smaroukis/Segments-2-the-absurd/kicad/00-Assets-Datasheets/2024-05-27-v-alpha/level-shifter_Texas-Instruments-TXS0108EPWR_C17206.pdf_FOOTPRINT.png

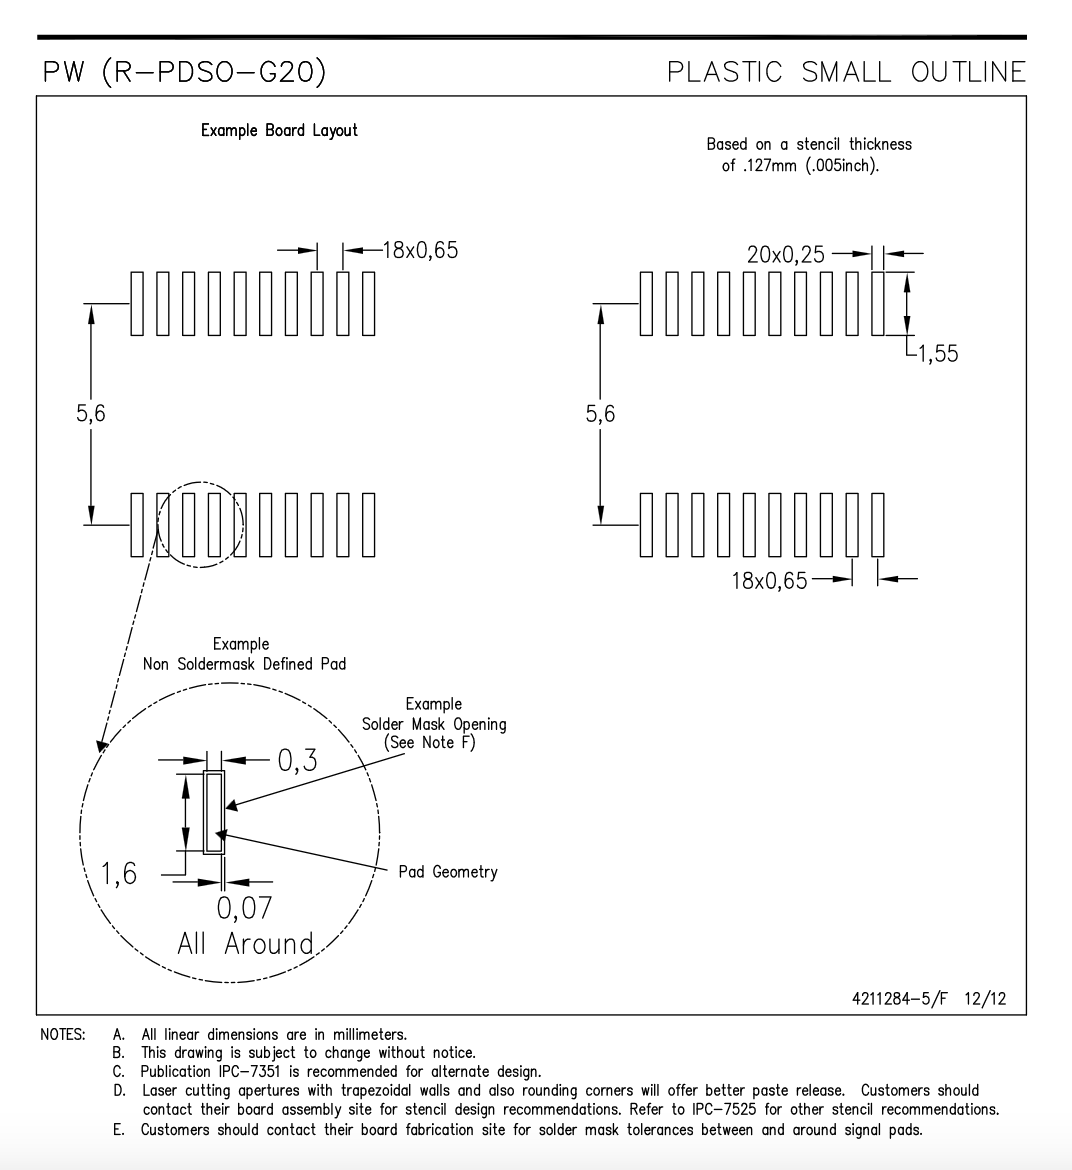
kicad/00-Assets-Datasheets/2024-05-27-v-alpha/level-shifter_Texas-Instruments-TXS0108EPWR_C17206.pdf_FOOTPRINT.png
