smaroukis/Segments-2-the-absurd/kicad/00-Assets-Datasheets/2024-05-27-v-alpha/mcu-STM32C011F6P6_C5456198_PACKAGE.png

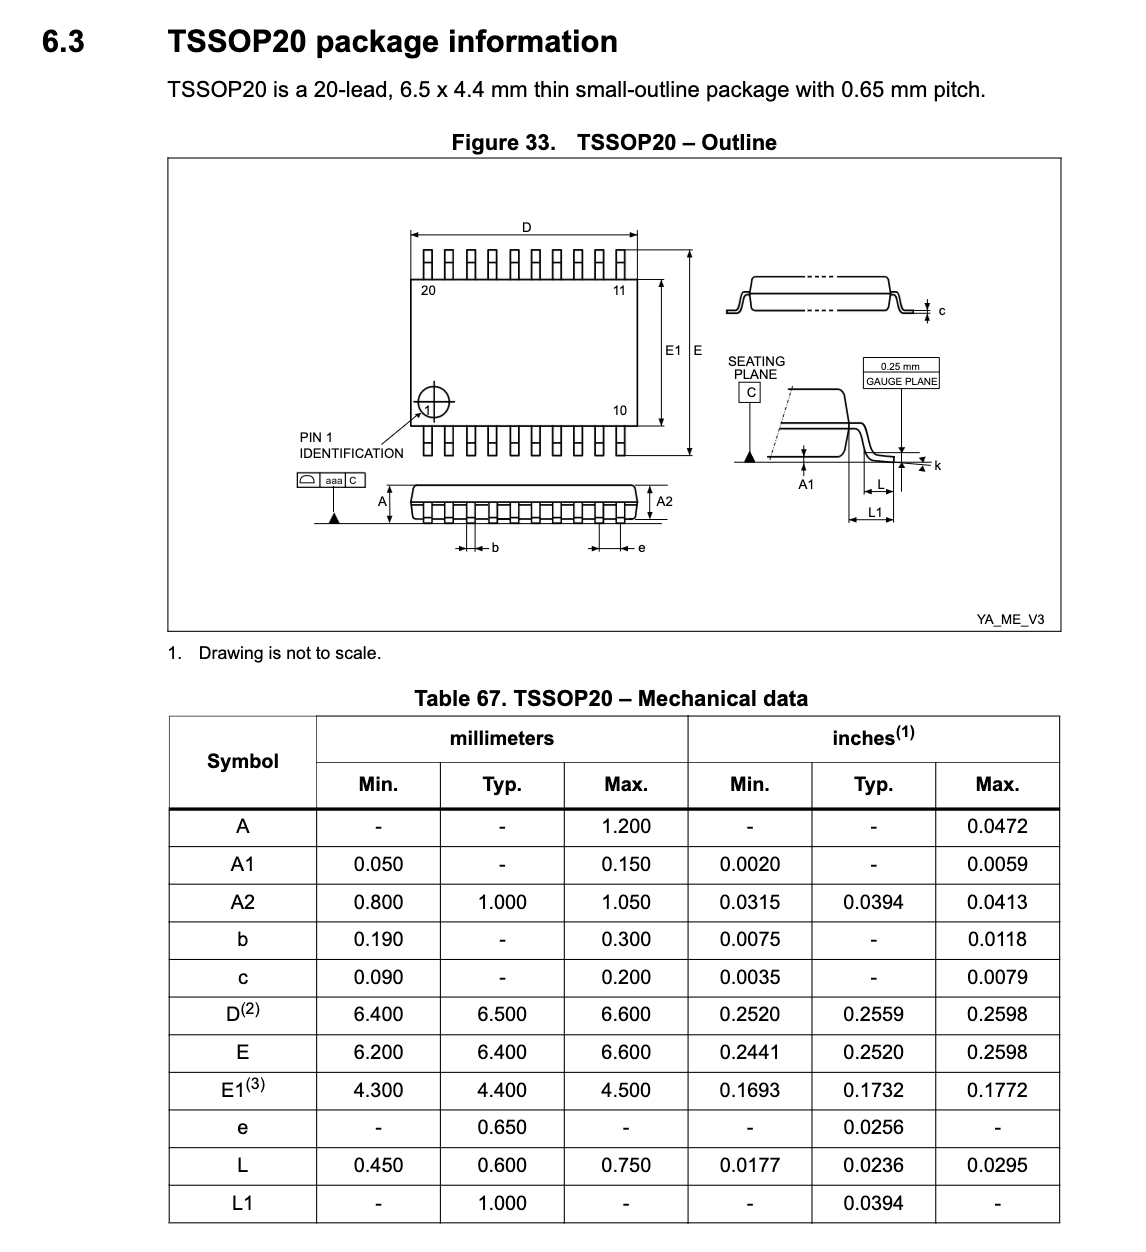
kicad/00-Assets-Datasheets/2024-05-27-v-alpha/mcu-STM32C011F6P6_C5456198_PACKAGE.png
