smaroukis/Segments-2-the-absurd/kicad/00-Assets-Datasheets/2024-05-27-v-alpha/sev-seg-driver_TM1637(TA2007)_FOOTPRINT.png

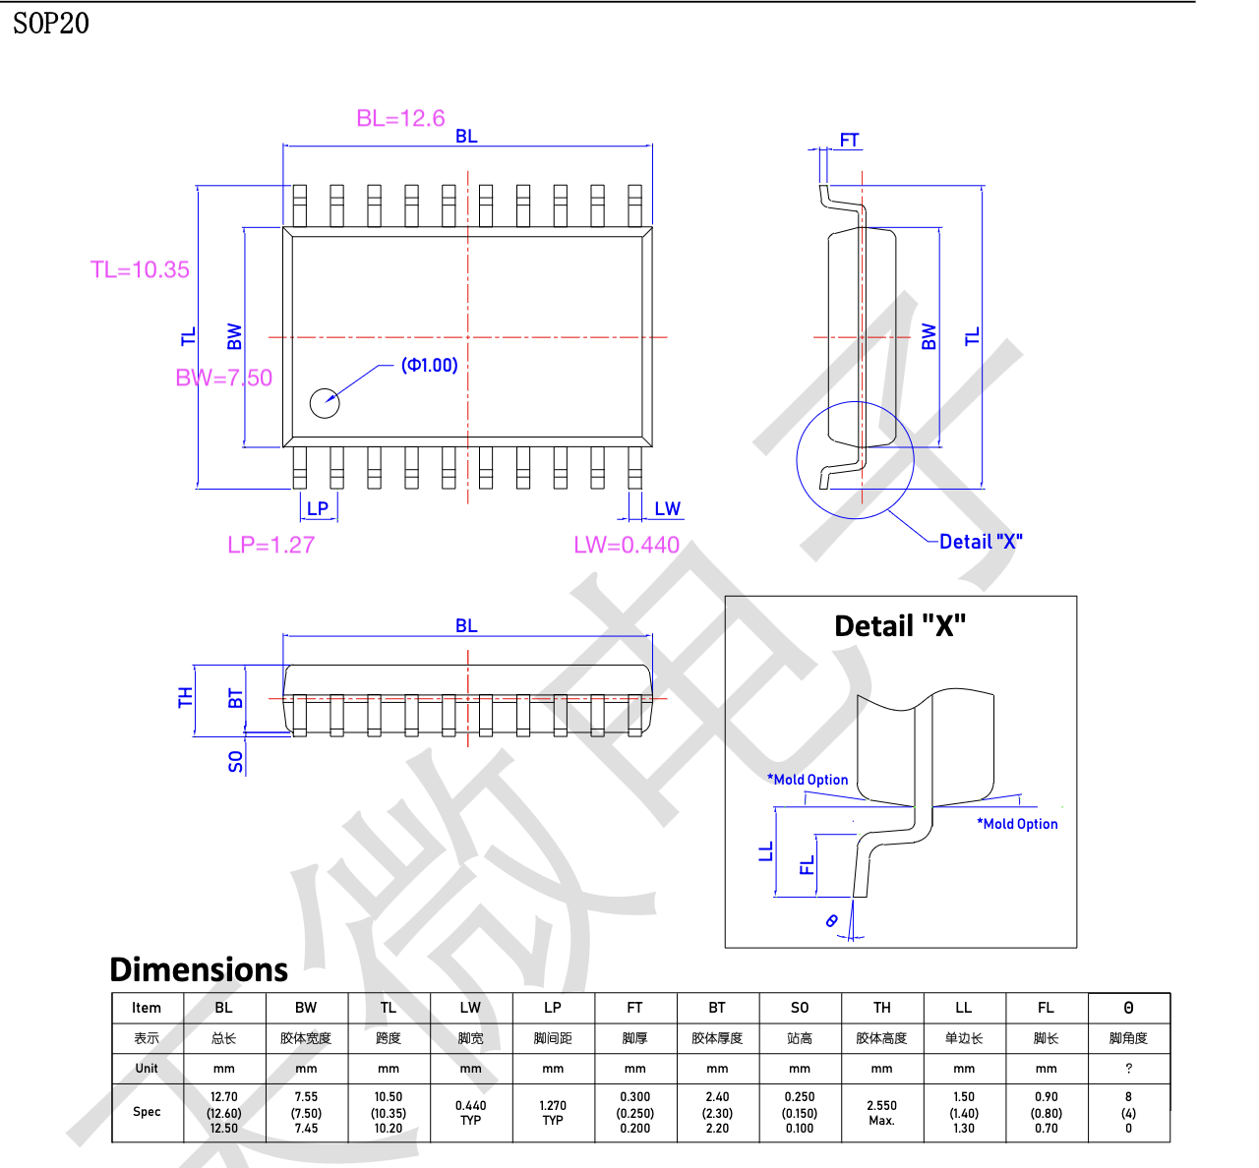
kicad/00-Assets-Datasheets/2024-05-27-v-alpha/sev-seg-driver_TM1637(TA2007)_FOOTPRINT.png
