smaroukis/Segments-2-the-absurd/kicad/00-Assets-Datasheets/2024-05-27-v-alpha/shift-register_2309131012_HXY-MOSFET-74HC595D_C5451631_FOOTPRINT.png

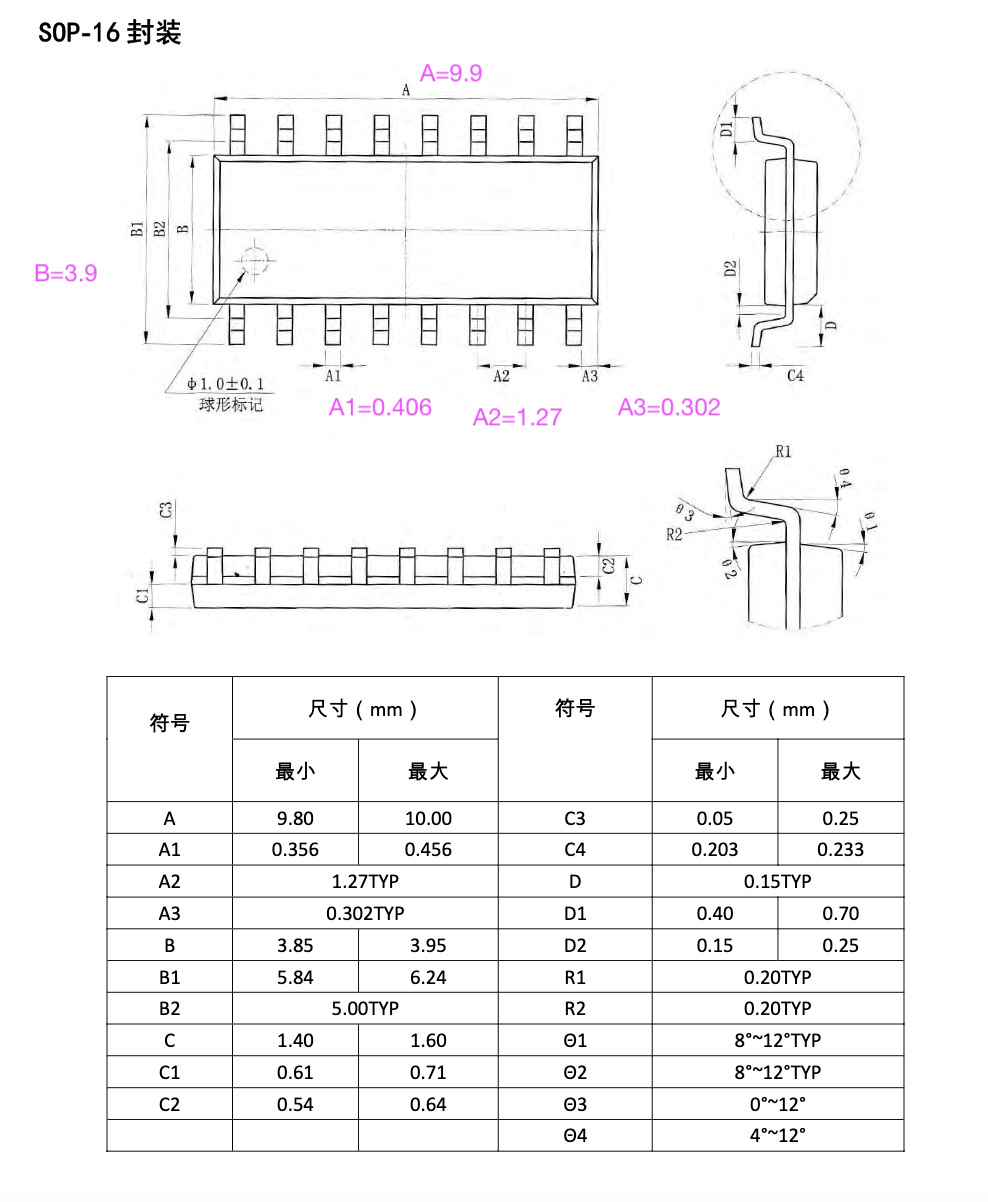
kicad/00-Assets-Datasheets/2024-05-27-v-alpha/shift-register_2309131012_HXY-MOSFET-74HC595D_C5451631_FOOTPRINT.png
